Quentin-33/esp8266-simple-rf-to-mqtt-gateway/IMAGES/IMG_20241123_174849.jpg

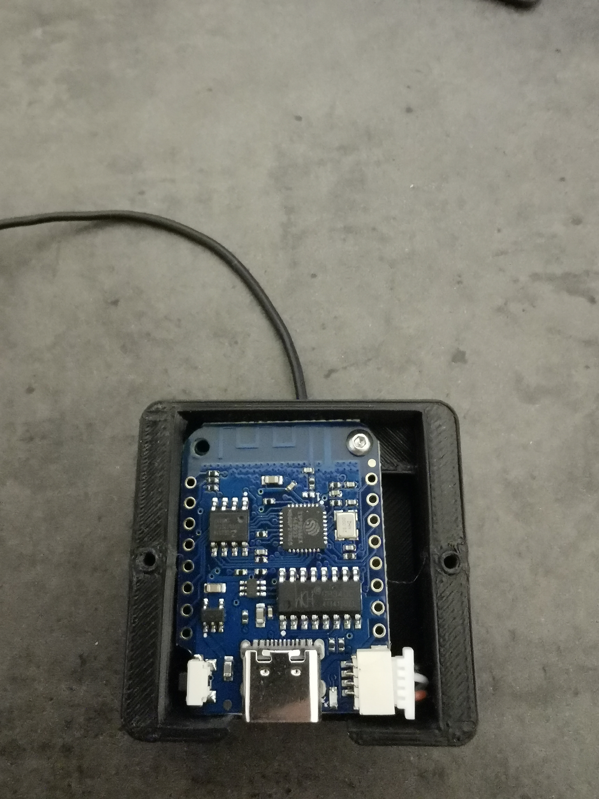
IMAGES/IMG_20241123_174849.jpg
